benchonaut/ULRICH-RADIG-DIMMERS/DMX-3channel/Bilder/DMX_Dimmer V2.JPG

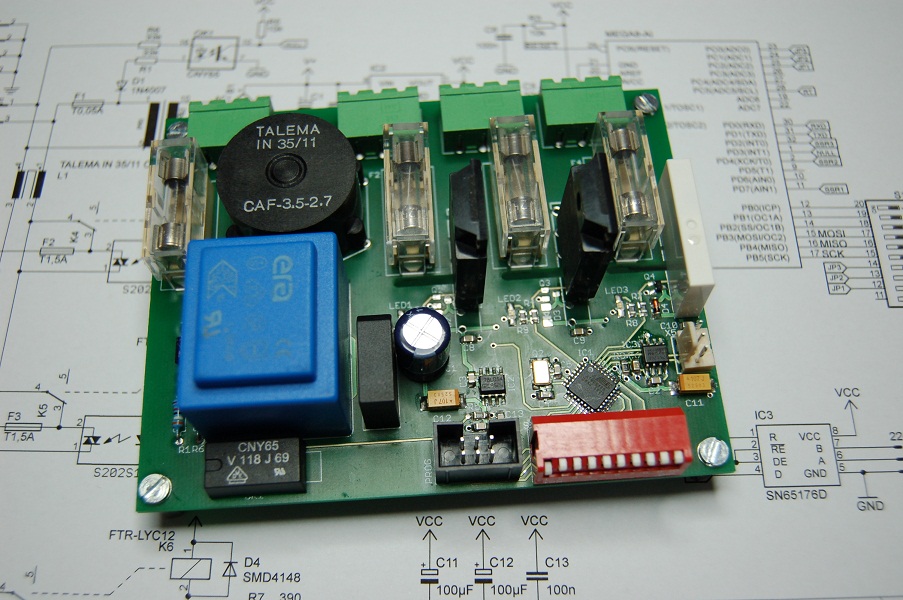
DMX-3channel/Bilder/DMX_Dimmer V2.JPG
