benchonaut/ULRICH-RADIG-DIMMERS/DMX-3channel/Bilder/DSC_0011.JPG

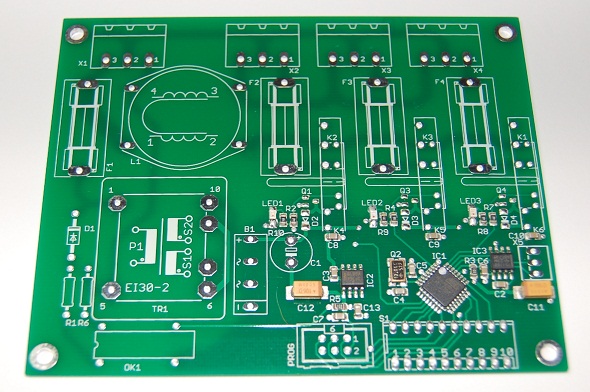
DMX-3channel/Bilder/DSC_0011.JPG
