benchonaut/ULRICH-RADIG-DIMMERS/DMX-3channel/Bilder/DSC_0014.JPG

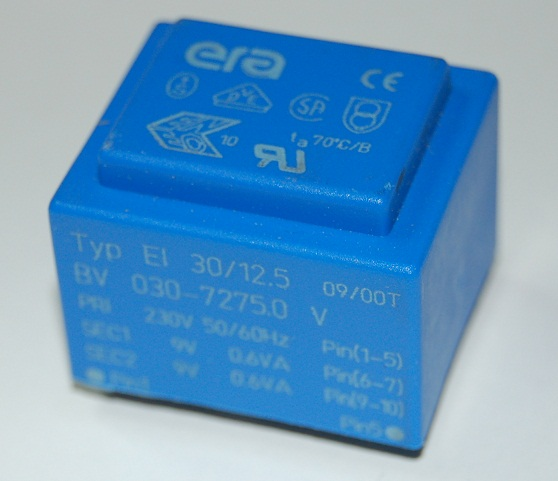
DMX-3channel/Bilder/DSC_0014.JPG
