benchonaut/ULRICH-RADIG-DIMMERS/DMX-3channel/Bilder/DSC_0019.JPG

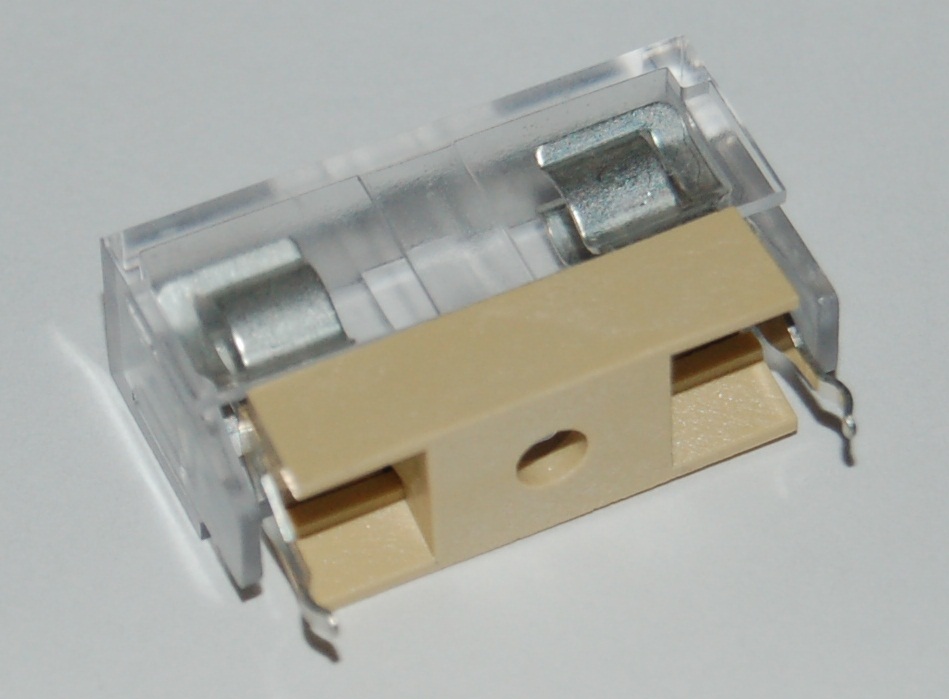
DMX-3channel/Bilder/DSC_0019.JPG
