benchonaut/ULRICH-RADIG-DIMMERS/DMX-3channel/LayoutV2/Bestueckung.png

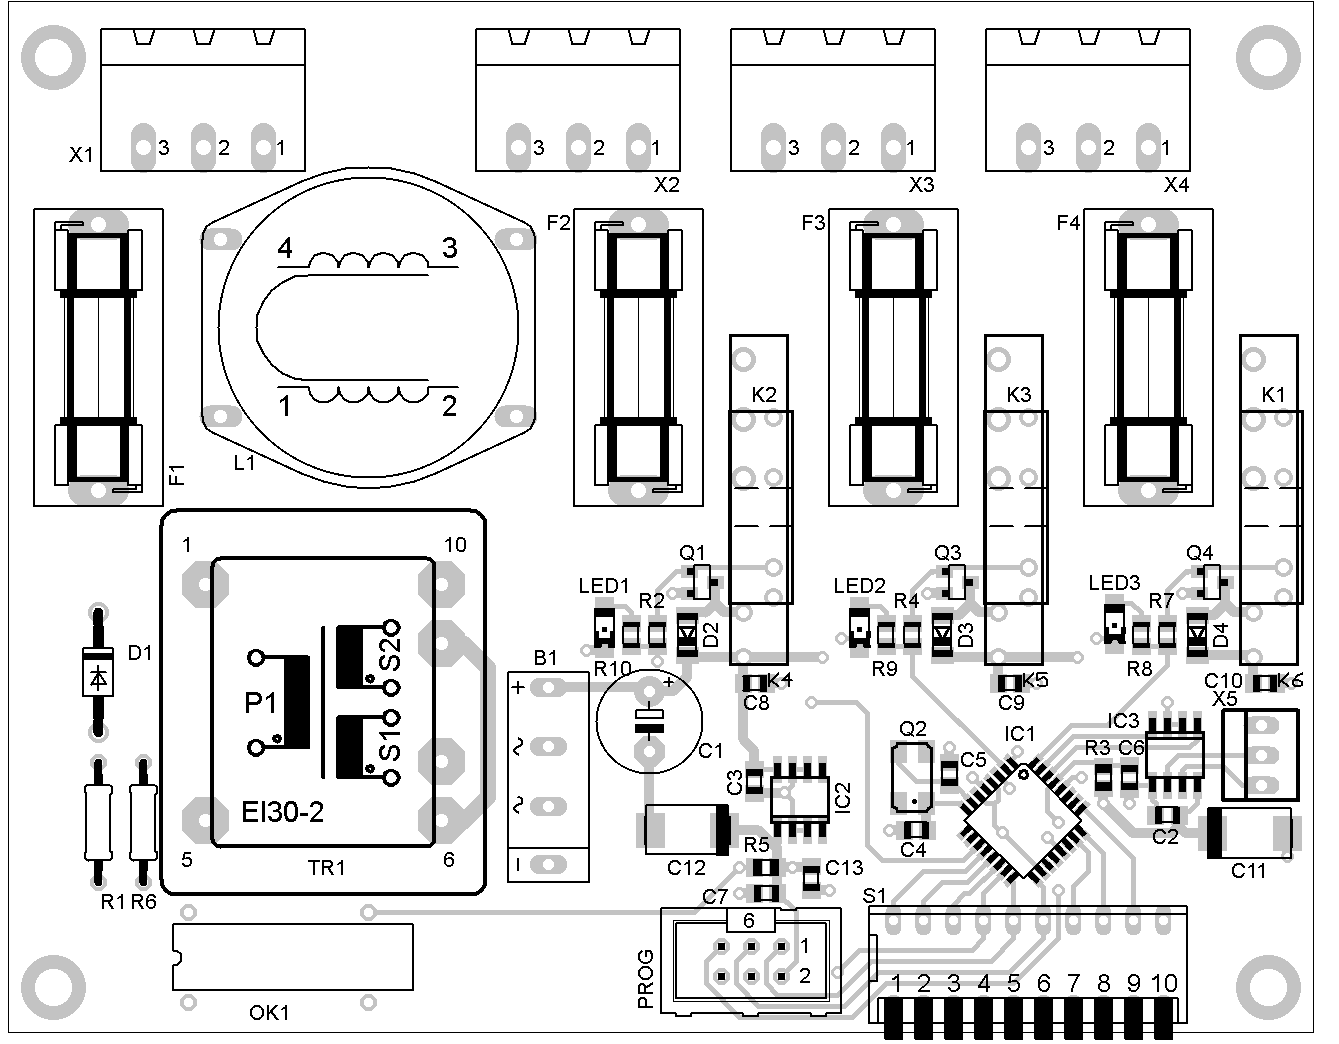
DMX-3channel/LayoutV2/Bestueckung.png
