benchonaut/ULRICH-RADIG-DIMMERS/DMX-8channel-V3/Bilder/DSC_0210.JPG

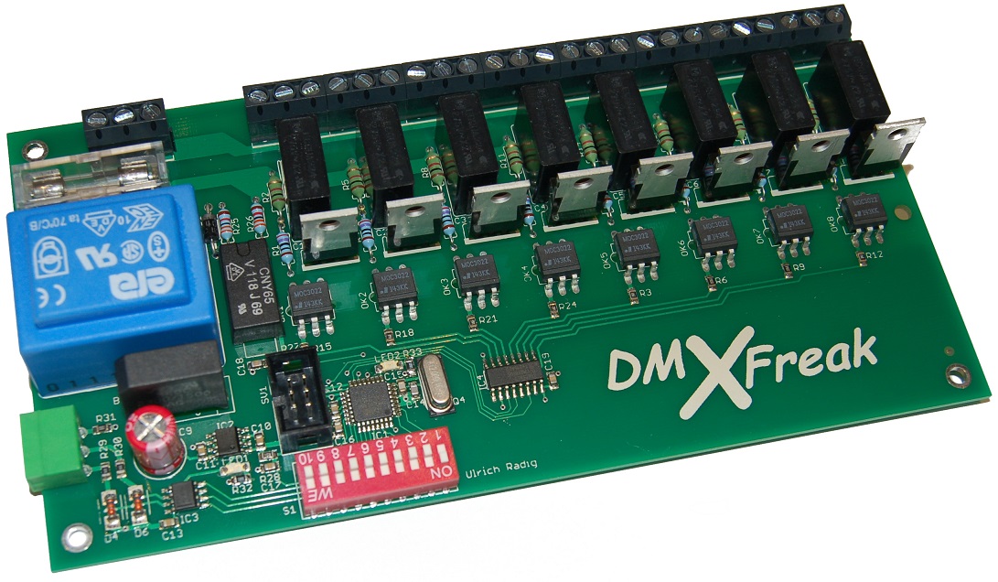
DMX-8channel-V3/Bilder/DSC_0210.JPG
