benchonaut/ULRICH-RADIG-DIMMERS/DMX-8channel-V3/Layout/Bestckung.png

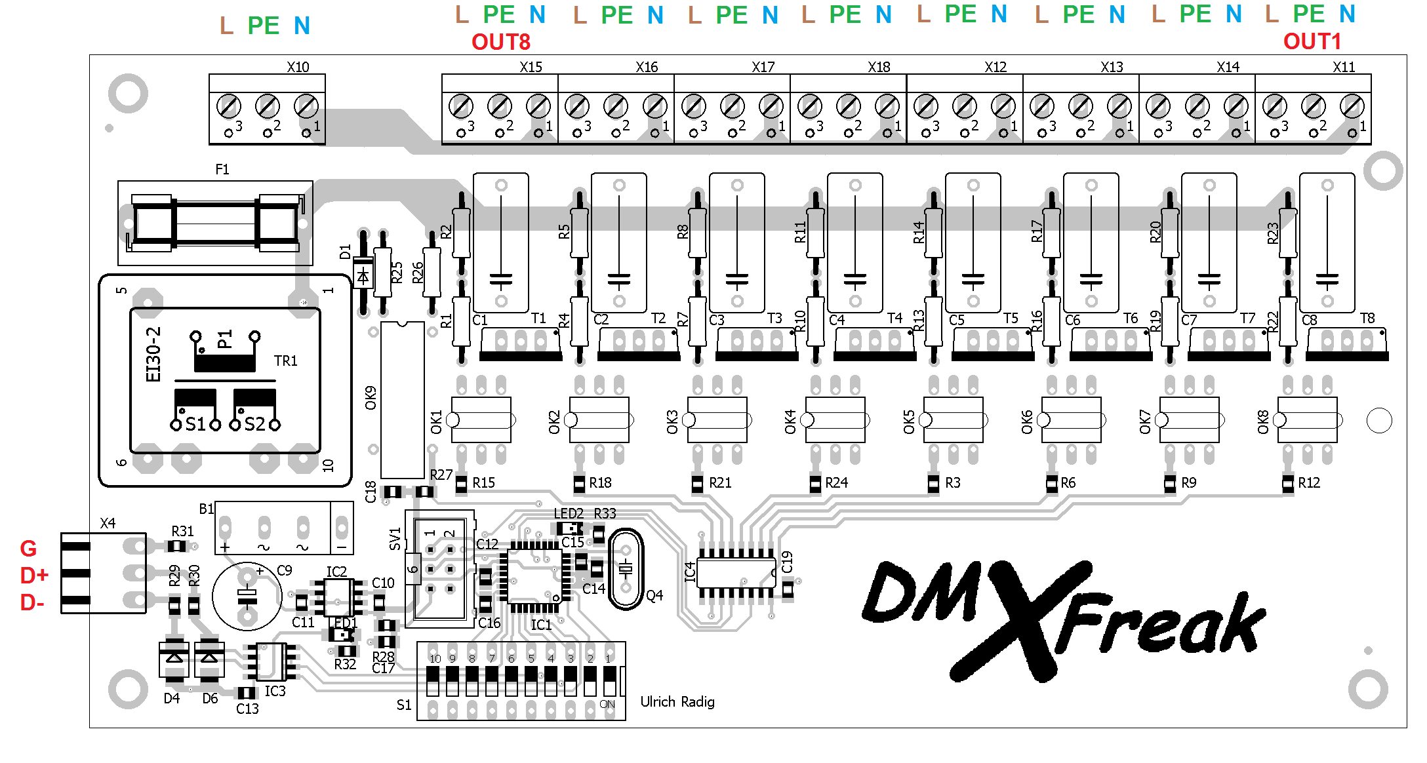
DMX-8channel-V3/Layout/Bestckung.png
